zaners123/rrisc/JavaAssembler/ArduinoProgrammer/hex.h

const uint8_t PROG[] PROGMEM = {
	0x06, 0x06, 0x9A, 0x8A, 0x06, 0x9C, 0x8C, 0x11, 0x0D, 0x06, 0x0B, 0x8A, 0x11, 0x0D, 0x06, 0x0B, 0x8A, 0x11, 0x0D, 0x06, 0x0B, 0x8A, 0x11, 0x0D, 0x06, 0x0B, 0x8A, 0x11, 0x0D, 0x06, 0x9A, 0x8A, 0x8B, 0x8C, 0x8B, 0x8C, 0x8B, 0x8C, 0x8B, 0x8C, 0x8B, 0x06, 0x9A, 0x8A, 0x2A, 0xFA, 0x06, 0x07, 0x07, 0xBA, 0x06, 0x77, 0x37, 0xAA, 0xFC, 0x2D, 0x11, 0x8A, 0xF5, 0x06, 0x21, 0x2A, 0x06, 0xF1, 0x3A, 0xFA, 0x06, 0x07, 0x07, 0xBA, 0x06, 0xC7, 0x47, 0xAA, 0xFC, 0x06, 0x20, 0x8A, 0xE4, 0x2D, 0xF5, 0x2C, 0x11, 0x2A, 0xFA, 0x06, 0x07, 0x07, 0xBA, 0x06, 0x17, 0x47, 0xAA, 0xFC, 0x32, 0xF5, 0xFA, 0x06, 0x07, 0x07, 0xBA, 0x06, 0xD7, 0x67, 0xAA, 0xFC, 0x06, 0x9A, 0x8A, 0x8C, 0x11, 0x8A, 0x1B, 0x65, 0x8C, 0x8C, 0x8C, 0x8C, 0x8C, 0x8C, 0x8C, 0x15, 
};
#define PROGNAME "primesieve23:53"
#define PROGSIZE 122
